ngsyst/bmp_boost_extender_mini/pcb/bmp-boost-extender-mini.kicad_sch

## KiCad design pcb/bmp-boost-extender-mini.kicad_sch (2026-02-23)

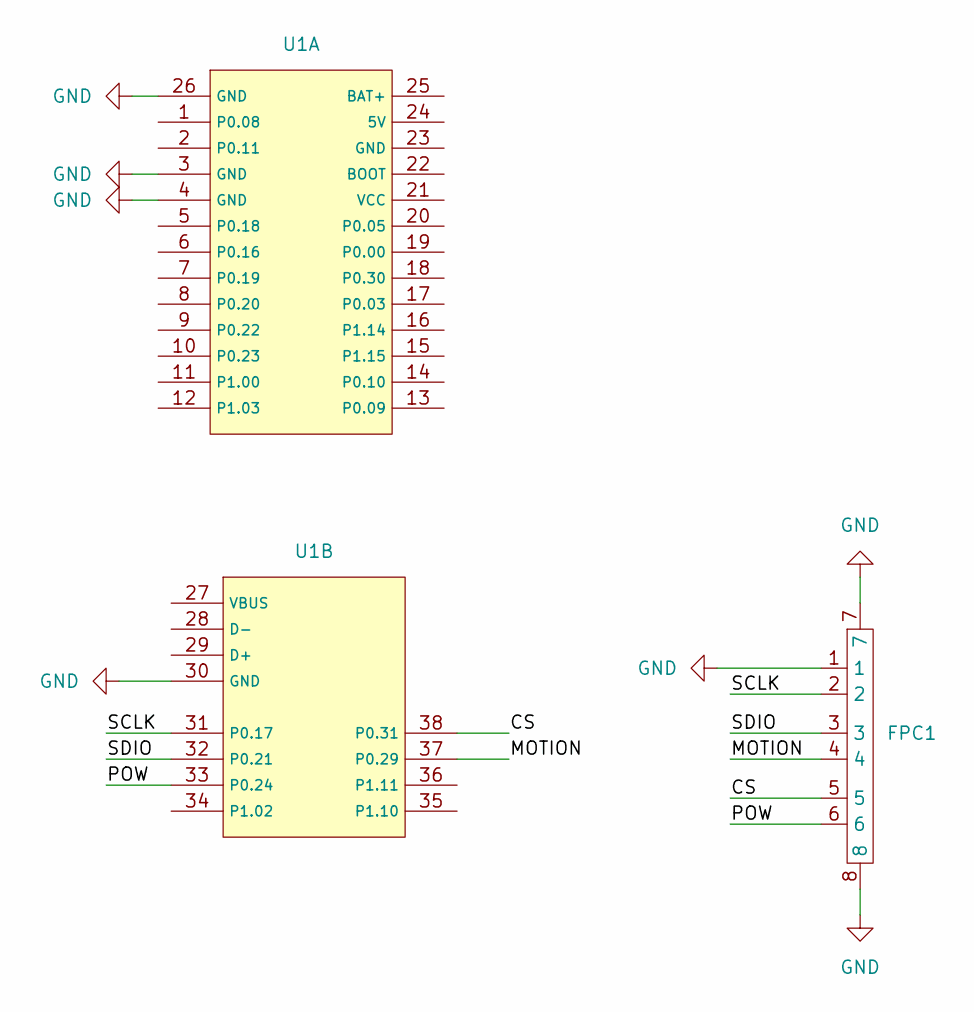
[picture p23: schematic bmp-boost-extender-mini.kicad_sch]

Parts:
FPC1: FPC-SMD_6P-P0.50_GT-F0501SR10-06S1101
U1: BMP-Boost-ext-mini

Connections:
CS: FPC1.5, U1.38 (P0.31)
GND: FPC1.1, FPC1.7, FPC1.8, U1.3 (GND), U1.4 (GND), U1.26 (GND), U1.30 (GND)
MOTION: FPC1.4, U1.37 (P0.29)
POW: FPC1.6, U1.33 (P0.24)
SCLK: FPC1.2, U1.31 (P0.17)
SDIO: FPC1.3, U1.32 (P0.21)
